MetrixLambert/smart-fan/0-report/pulse/fig/design/design0.png

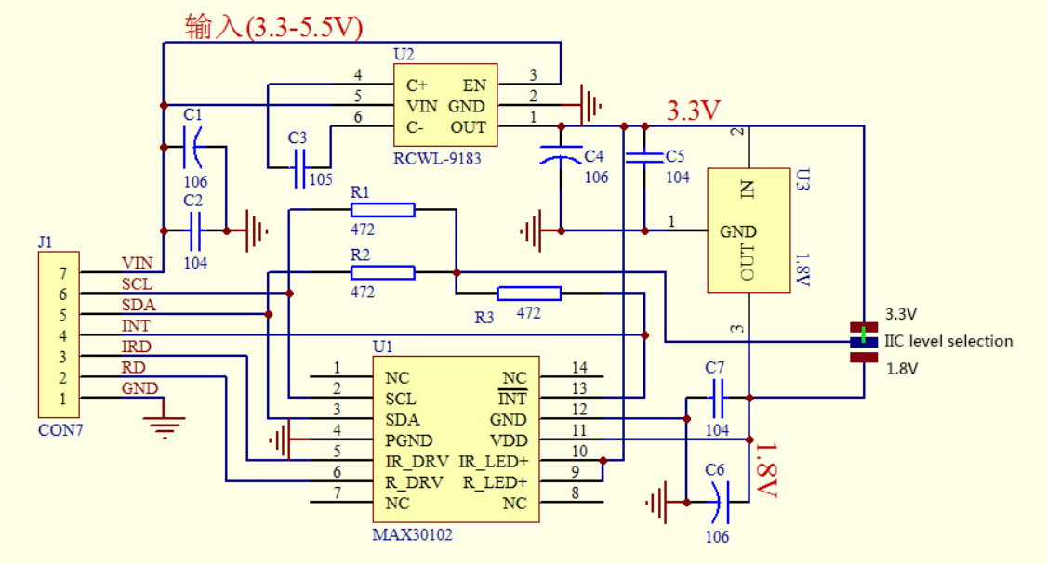
0-report/pulse/fig/design/design0.png
