MetrixLambert/smart-fan/0-report/smartfan/fig/sim/sim4_result1.png

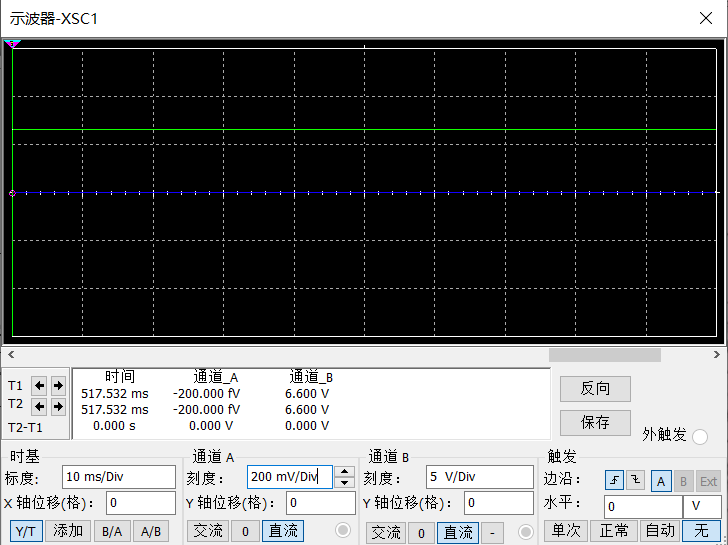
0-report/smartfan/fig/sim/sim4_result1.png
